teapotlaboratories/plantpal/docs/images/back_resin.jpg

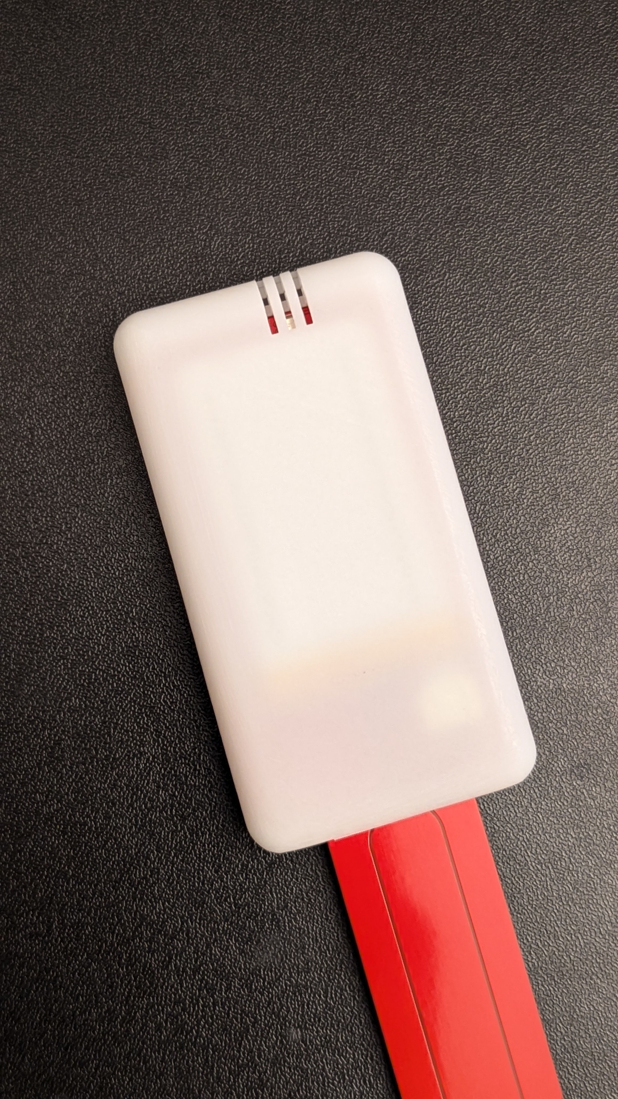
docs/images/back_resin.jpg
