teapotlaboratories/plantpal/docs/images/device_resin.jpg

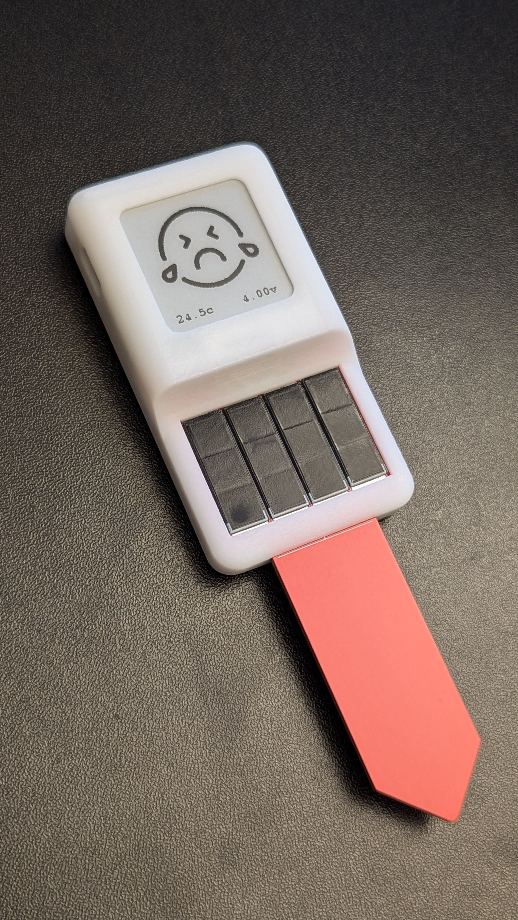
docs/images/device_resin.jpg
