teapotlaboratories/plantpal/docs/images/environmental_sensor_closeup_resin.jpg

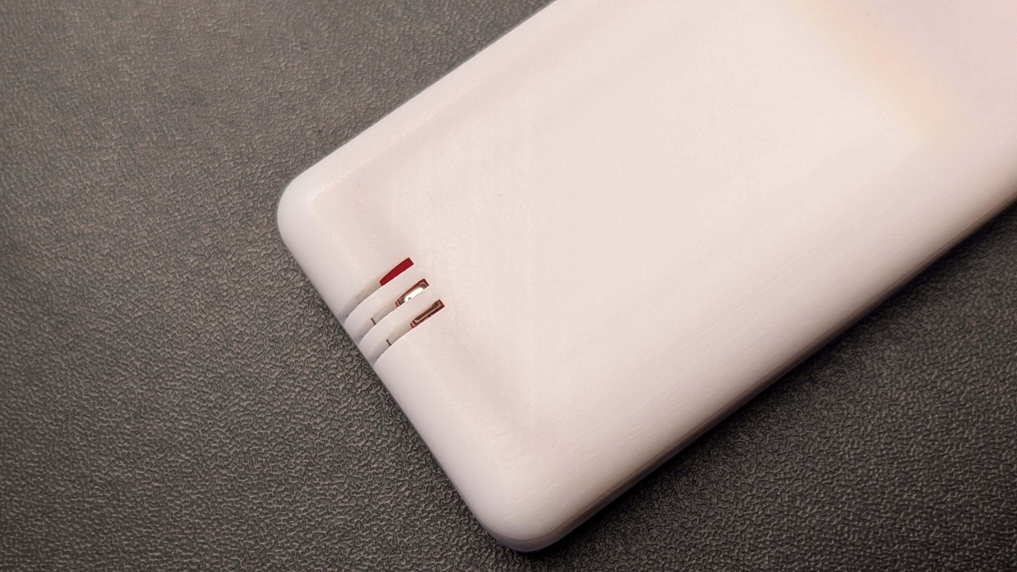
docs/images/environmental_sensor_closeup_resin.jpg
