teapotlaboratories/plantpal/docs/images/front_closeup_resin.jpg

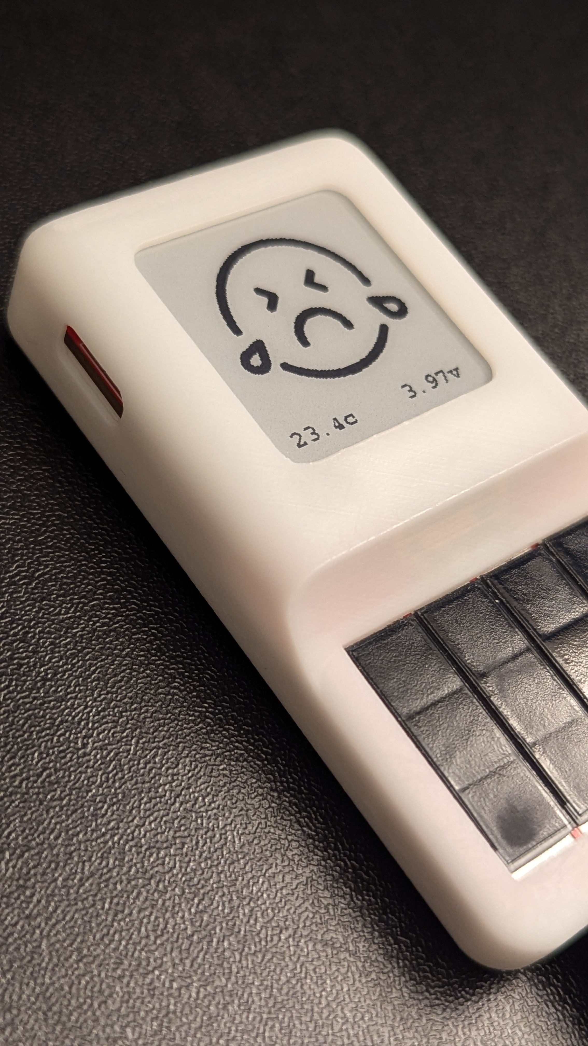
docs/images/front_closeup_resin.jpg
