teapotlaboratories/plantpal/docs/images/front_resin.jpg

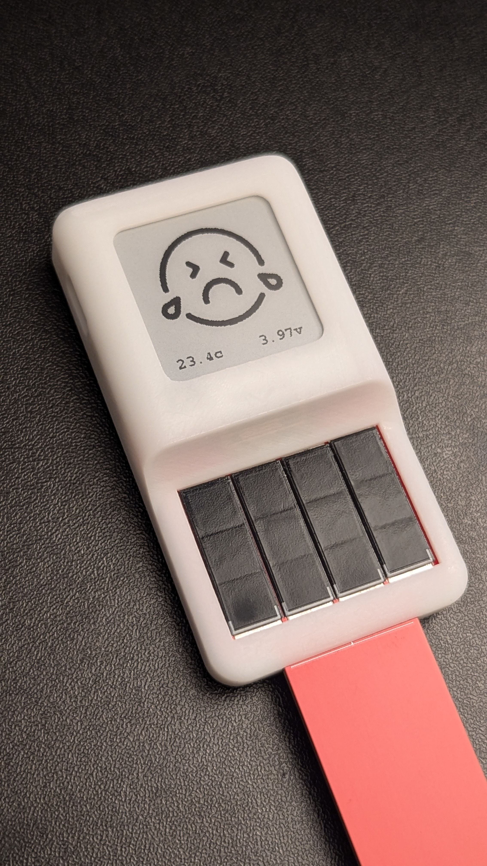
docs/images/front_resin.jpg
