teapotlaboratories/plantpal/docs/images/side_left_resin.jpg

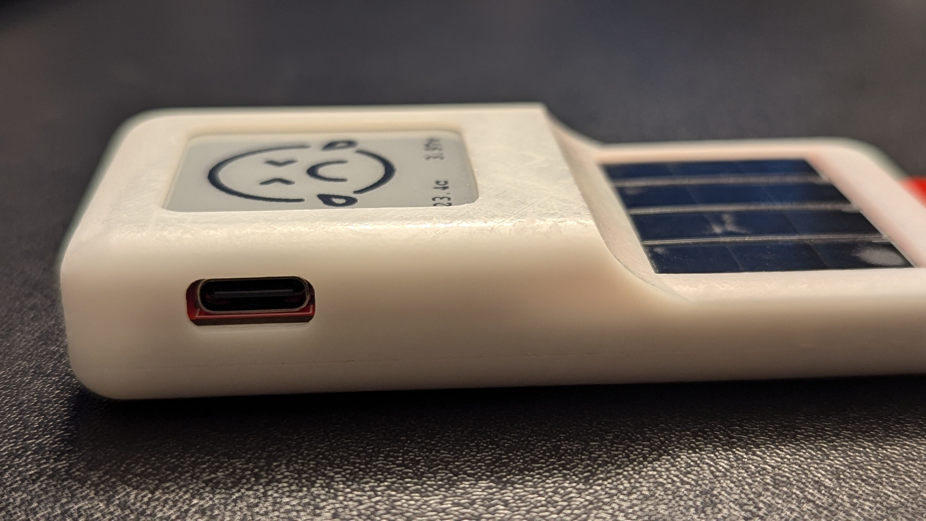
docs/images/side_left_resin.jpg
