teapotlaboratories/plantpal/docs/images/side_right_resin.jpg

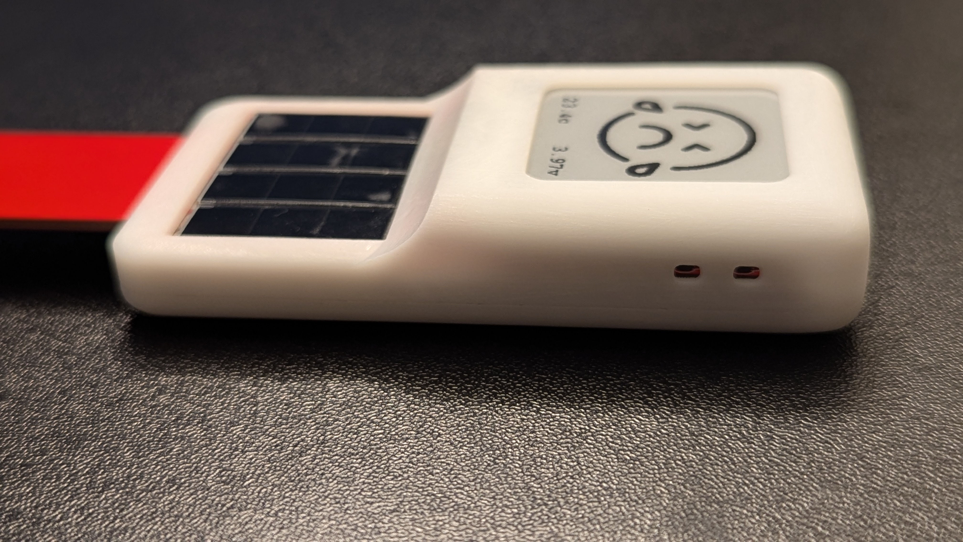
docs/images/side_right_resin.jpg
